sparkfun/SparkFun_Buck_Regulator_AP3429A/docs/img/hookup_guide/1V8-bottom.jpg

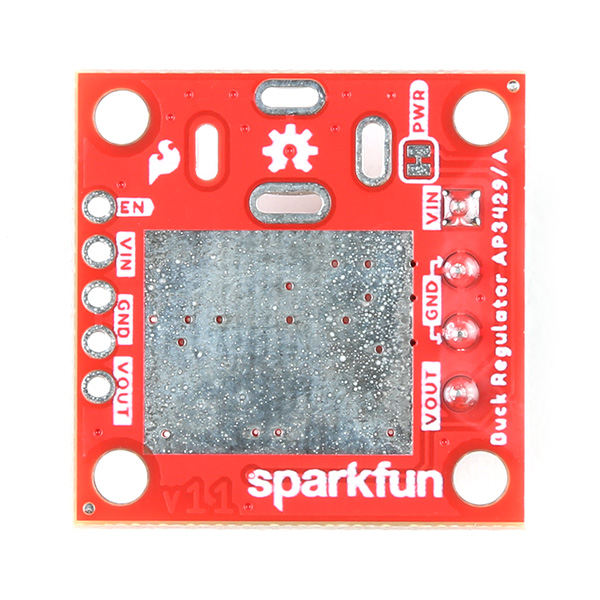
docs/img/hookup_guide/1V8-bottom.jpg
