sparkfun/SparkFun_Buck_Regulator_AP3429A/docs/img/hookup_guide/3V3-top.jpg

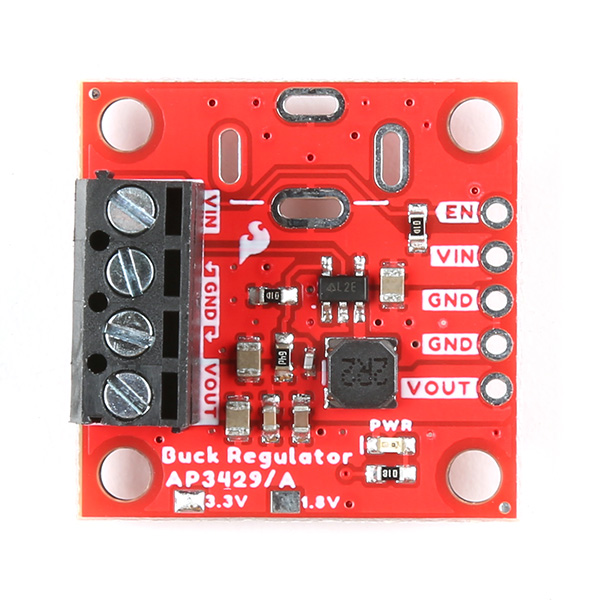
docs/img/hookup_guide/3V3-top.jpg
